Minho62/3D_Mapping_MICCA/img/car_PCB_page-0003.jpg

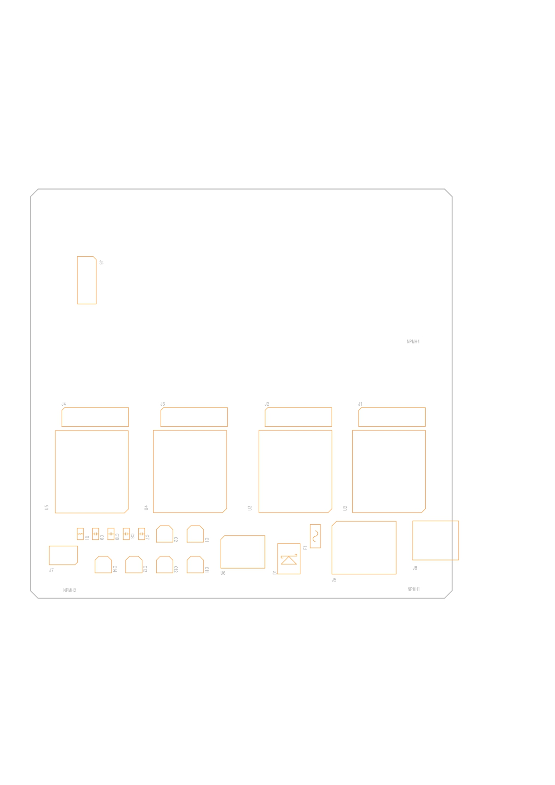
img/car_PCB_page-0003.jpg
