Minho62/3D_Mapping_MICCA/img/CAVE2.jpg

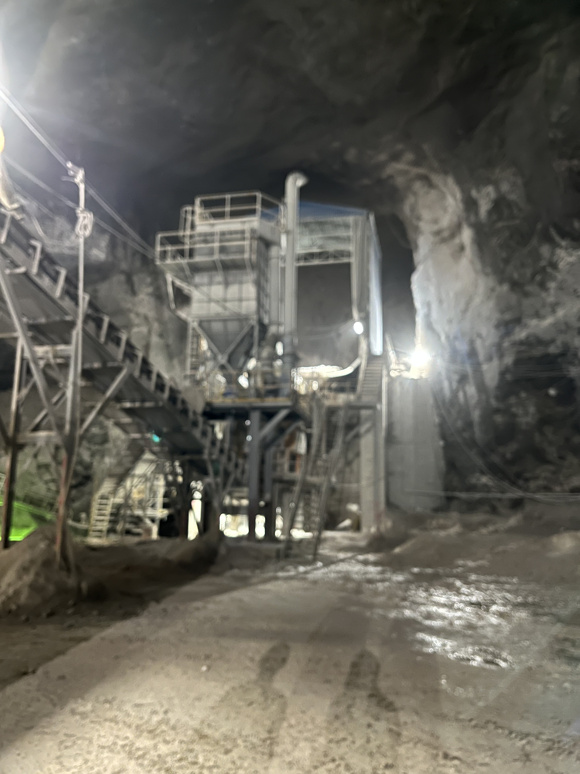
img/CAVE2.jpg
