Minho62/3D_Mapping_MICCA/img/control_box_PCB_page-0004.jpg

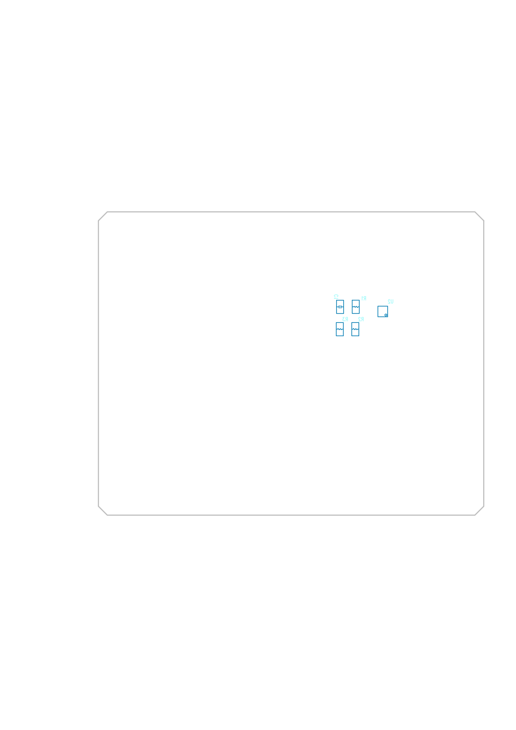
img/control_box_PCB_page-0004.jpg
