Minho62/3D_Mapping_MICCA/img/TUNNEL2.png

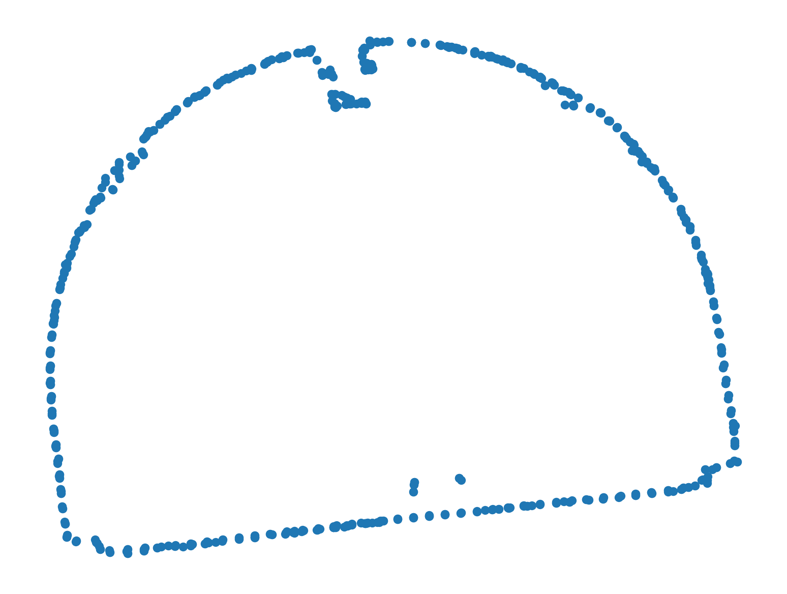
img/TUNNEL2.png
