Minho62/3D_Mapping_MICCA/doc/SD50.pdf

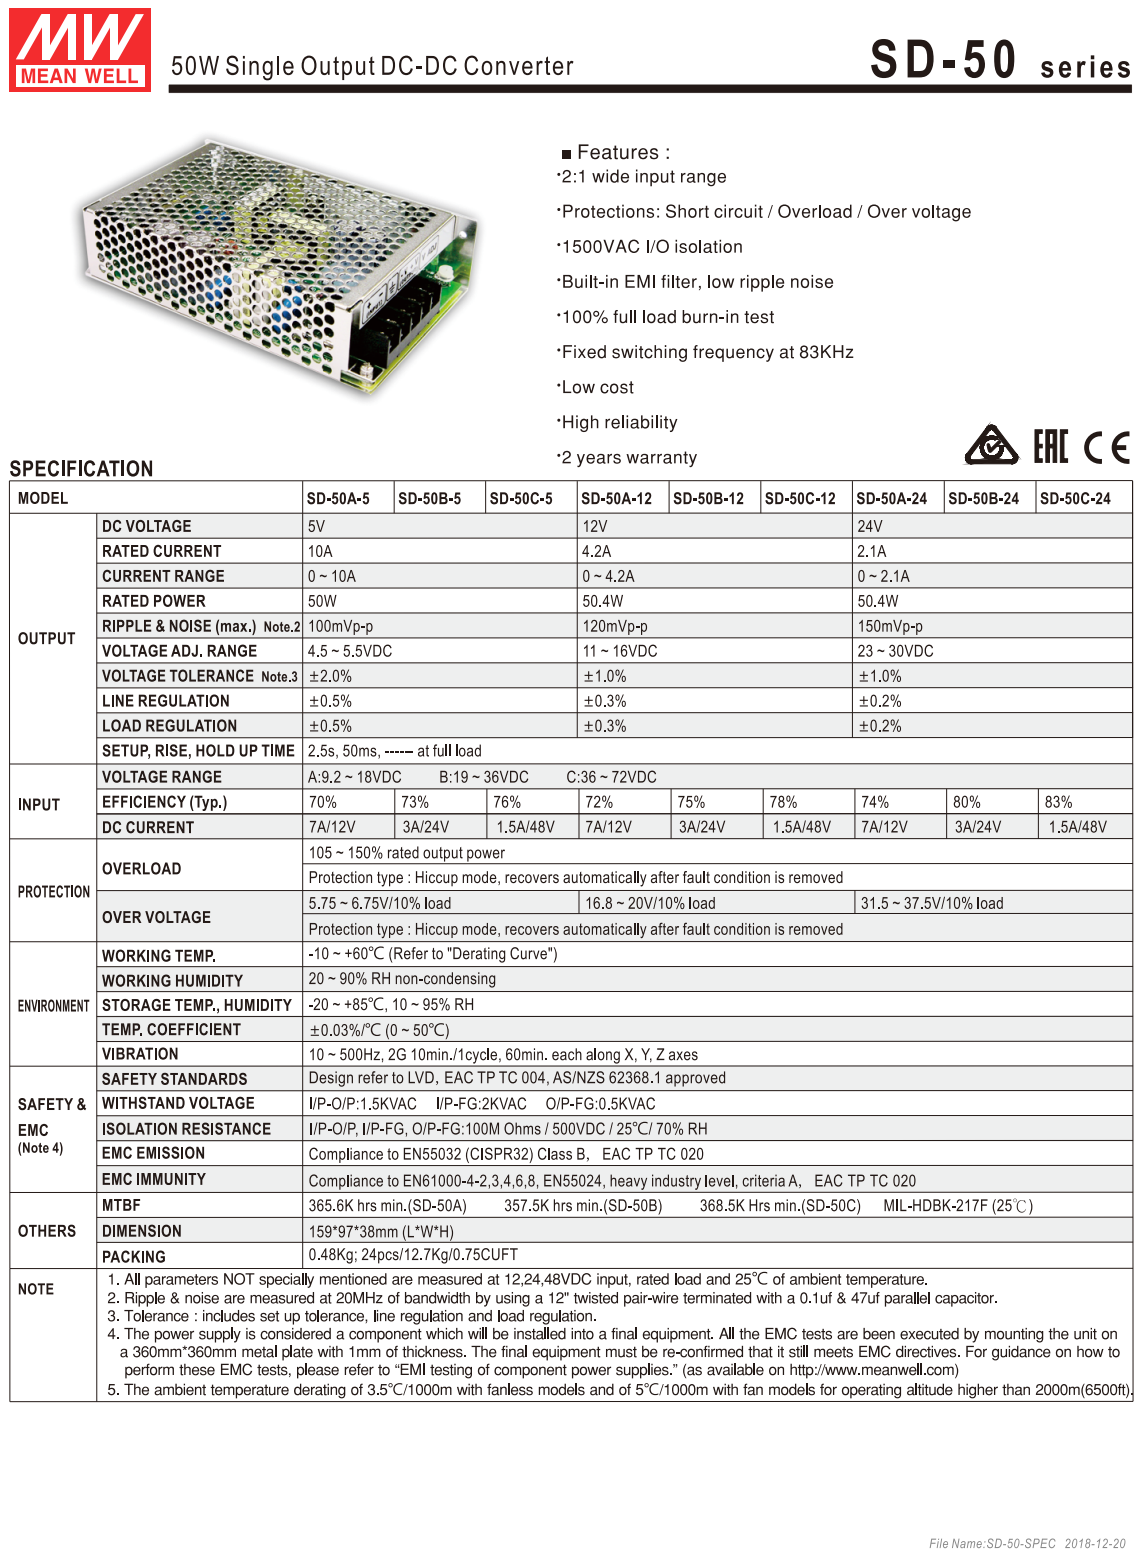
[picture p75: page 1]

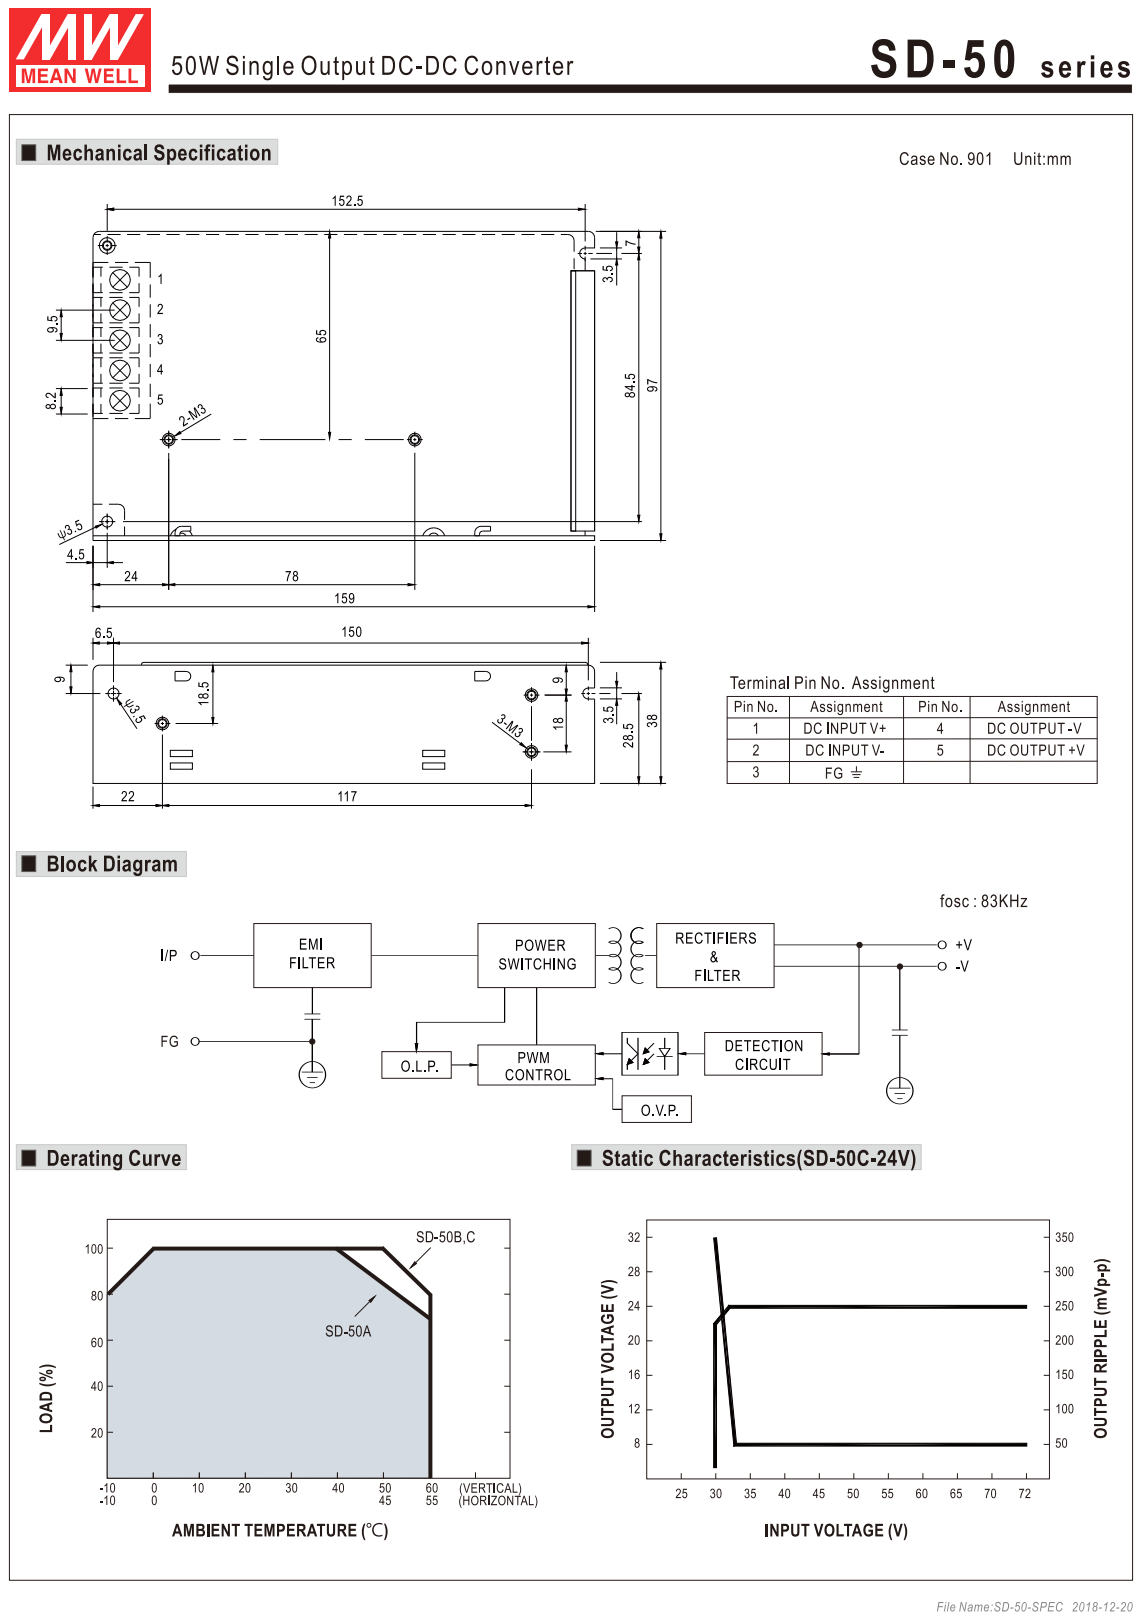
[picture p76: page 2]
