Minho62/3D_Mapping_MICCA/img/CAVE0.jpg

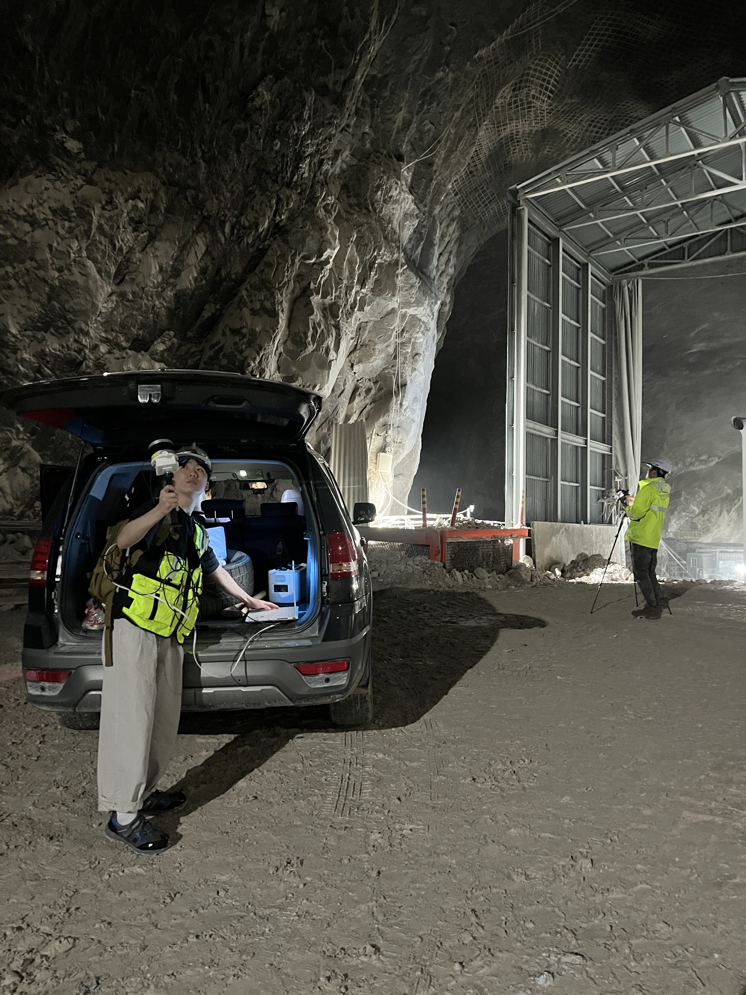
img/CAVE0.jpg
